lucasliano/td2project/diagrama/buzzer.png

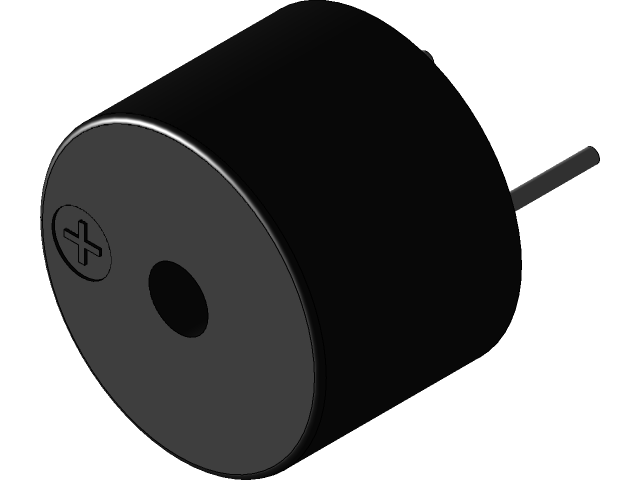
diagrama/buzzer.png
