lucasliano/td2project/diagrama/Chip RFID.png

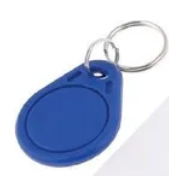
diagrama/Chip RFID.png
