lucasliano/td2project/diagrama/Diagrama-General.jpeg

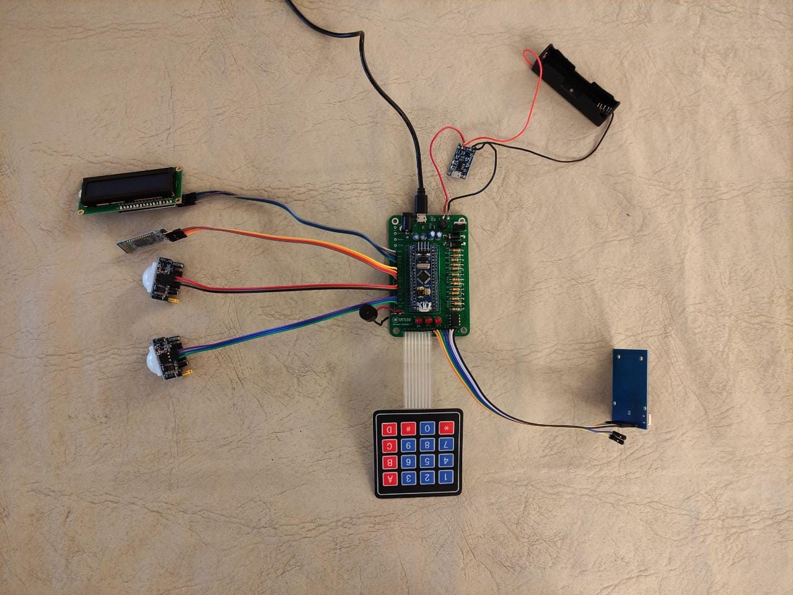
diagrama/Diagrama-General.jpeg
