lucasliano/td2project/diagrama/Diagrama-General.png

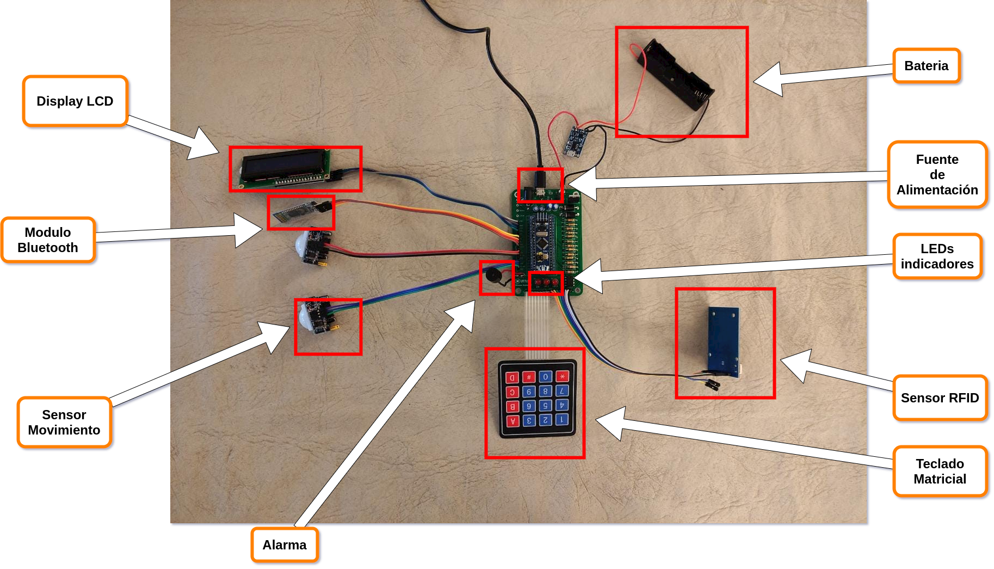
diagrama/Diagrama-General.png
