lucasliano/td2project/diagrama/Diagrama.png

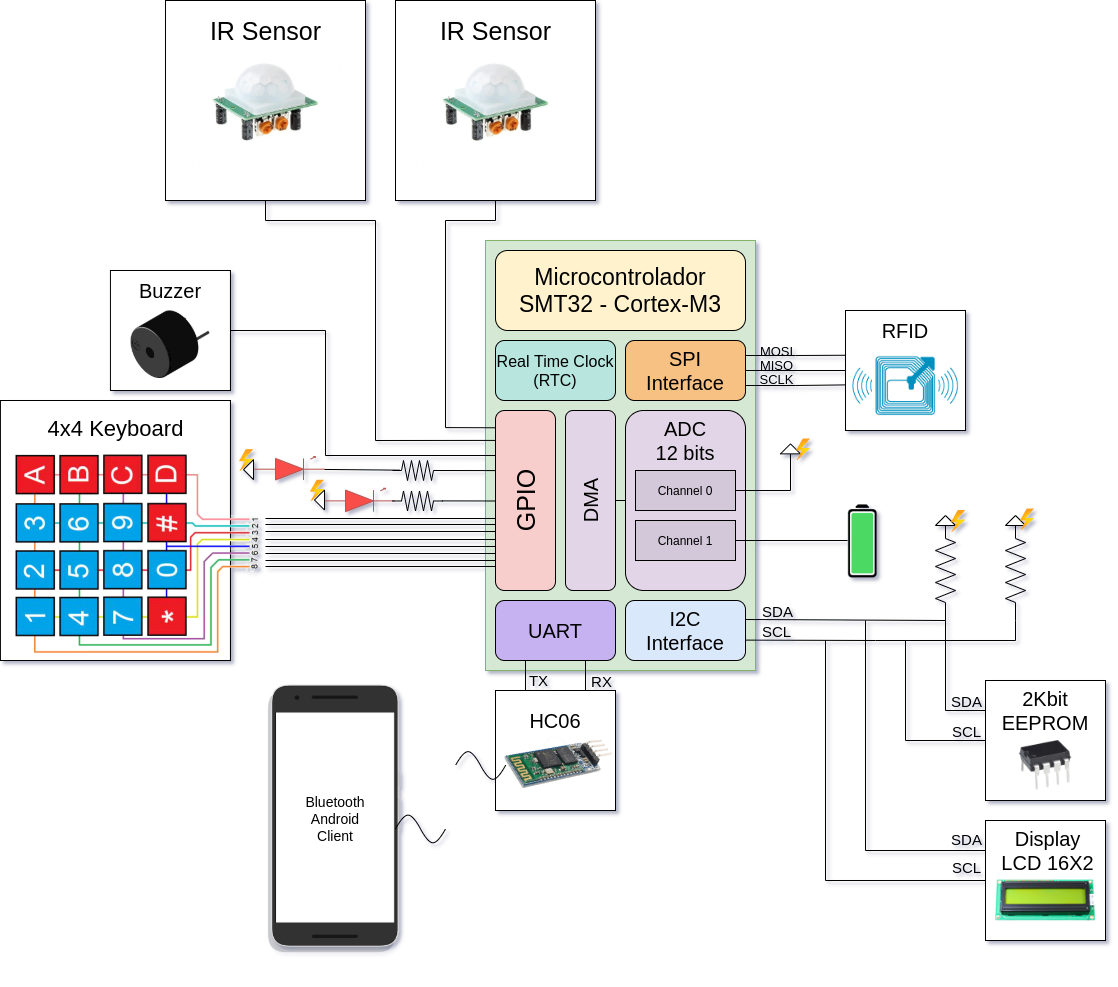
diagrama/Diagrama.png
