lucasliano/td2project/diagrama/fsm_global.png

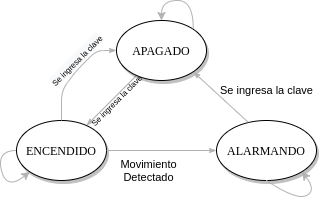
diagrama/fsm_global.png
