lucasliano/td2project/diagrama/get_mem.png

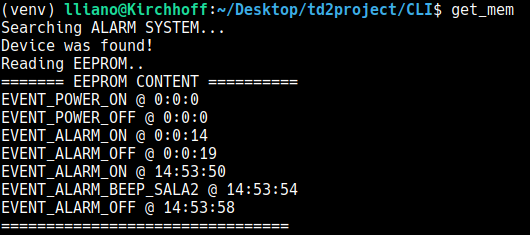
diagrama/get_mem.png
