lucasliano/td2project/diagrama/LCD.png

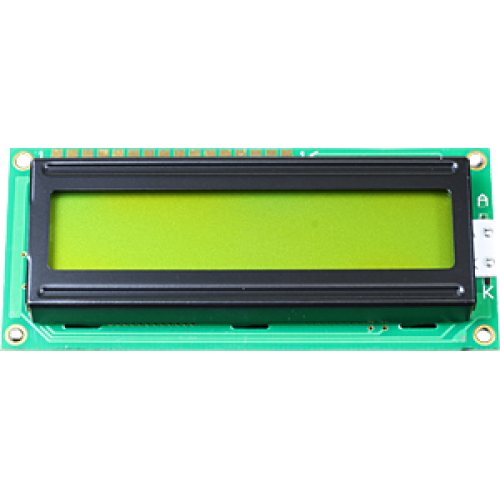
diagrama/LCD.png
