lucasliano/td2project/diagrama/MT3608.png

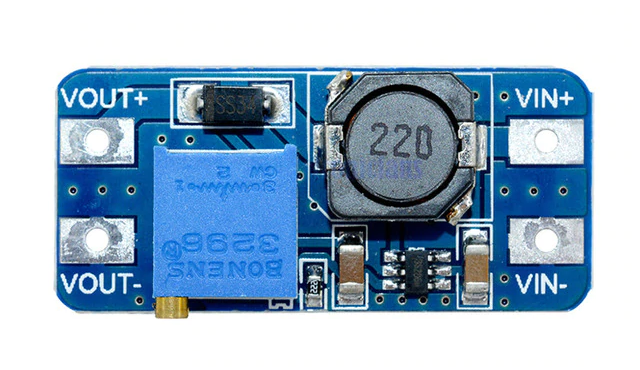
diagrama/MT3608.png
