lucasliano/td2project/diagrama/PCB-cool.jpeg

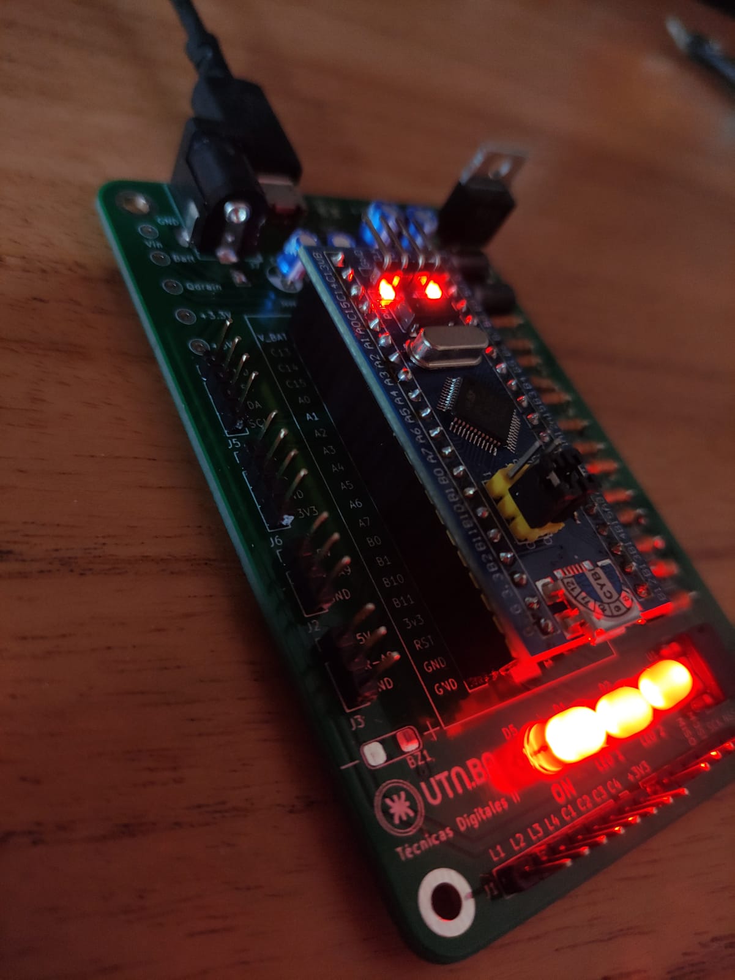
diagrama/PCB-cool.jpeg
