lucasliano/td2project/diagrama/pcb_back.png

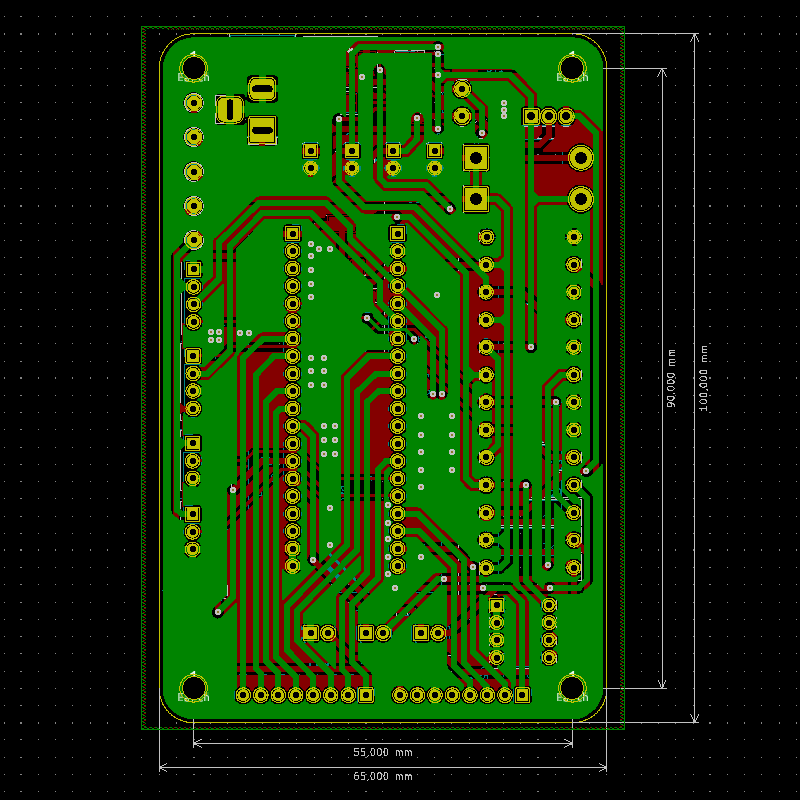
diagrama/pcb_back.png
