lucasliano/td2project/diagrama/pcb_front.png

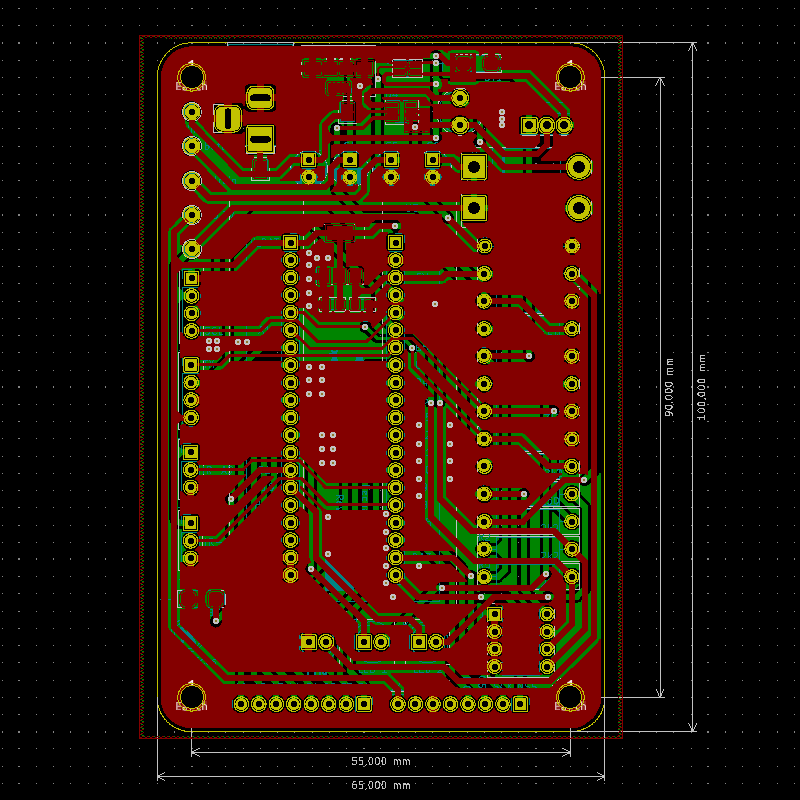
diagrama/pcb_front.png
