lucasliano/td2project/diagrama/Sensor.png

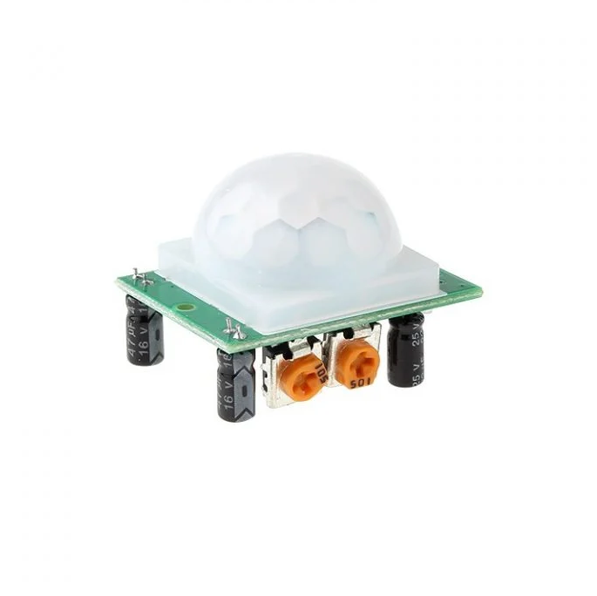
diagrama/Sensor.png
