lucasliano/td2project/diagrama/STM32.png

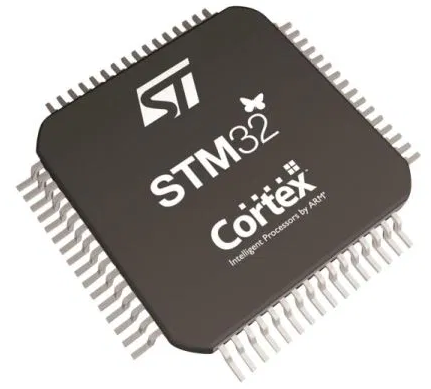
diagrama/STM32.png
