lucasliano/td2project/PCB/Comportamiento Q1.png

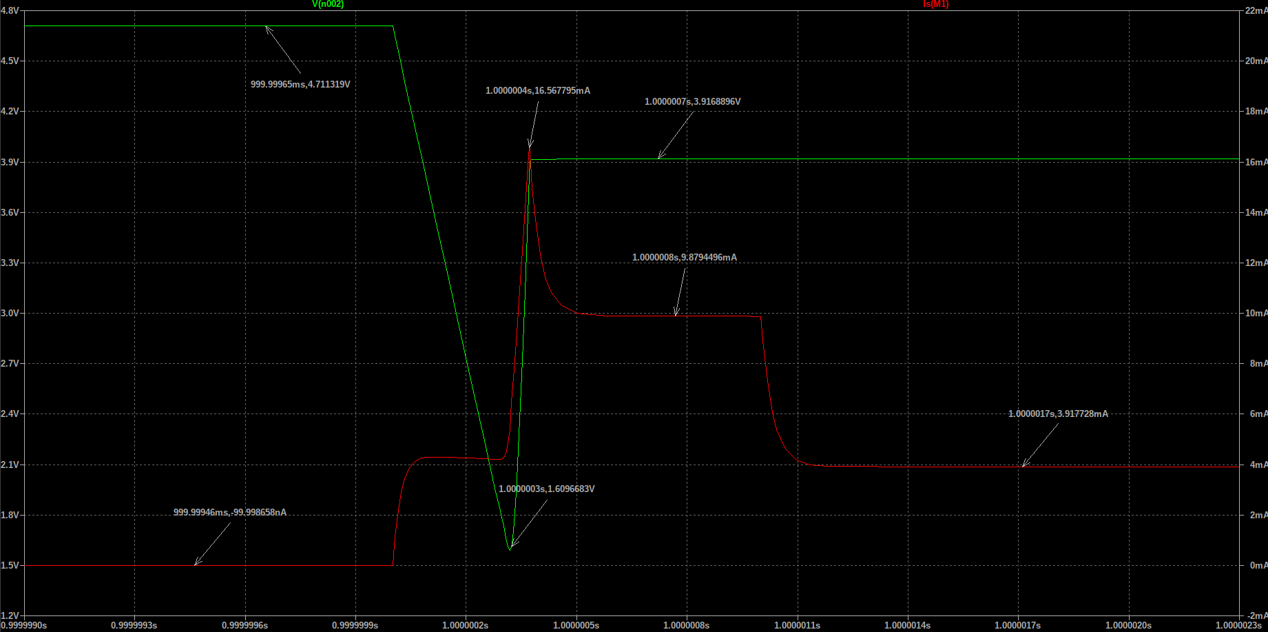
PCB/Comportamiento Q1.png
