lucasliano/td2project/PCB/project/vout_formula.png

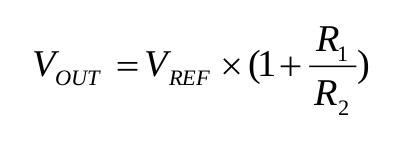
PCB/project/vout_formula.png
