lucasliano/td2project/software/Core/Inc/own_drivers.h

/**
  ******************************************************************************
  * @file           : own_drivers.h
  * @brief          : Llama a los includes de los drivers propios.
  ******************************************************************************
**/

/* Define to prevent recursive inclusion -------------------------------------*/
#ifndef __OWN_DRIVERS_H
#define __OWN_DRIVERS_H
#include <adc.h>
#include <arrebote.h>
#include <arrebote.h>
#include <eeprom.h>
#include <gpio.h>
#include <lcd.h>
#include <MFRC522.h>
#include <rtc.h>
#include <sensor.h>
#include <stdlib.h>
#include <stdio.h>
#include <string.h>
#include <hc05.h>

#include <teclado.h>

#endif /* __OWN_DRIVERS_H */
