lucasliano/td2project/software/Core/Inc/MFRC522.h

#ifndef MFRC522_H_
#define MFRC522_H_

#include "main.h"
#include "stm32f1xx_hal.h"
#include <sys/types.h>

#define SPI_NSS_Pin GPIO_PIN_12
#define SPI_NSS_GPIO_Port GPIOB

//Maximum length of the array
#define MAX_LEN 16

//MF522 Command word
#define PCD_IDLE              0x00               //NO action; Cancel the current command
#define PCD_AUTHENT           0x0E               //Authentication Key
#define PCD_RECEIVE           0x08               //Receive Data
#define PCD_TRANSMIT          0x04               //Transmit data
#define PCD_TRANSCEIVE        0x0C               //Transmit and receive data,
#define PCD_RESETPHASE        0x0F               //Reset
#define PCD_CALCCRC           0x03               //CRC Calculate

// Mifare_One card command word
# define PICC_REQIDL          0x26               // find the antenna area does not enter hibernation
# define PICC_REQALL          0x52               // find all the cards antenna area
# define PICC_ANTICOLL        0x93               // anti-collision
# define PICC_SElECTTAG       0x93               // election card
# define PICC_AUTHENT1A       0x60               // authentication key A
# define PICC_AUTHENT1B       0x61               // authentication key B
# define PICC_READ            0x30               // Read Block
# define PICC_WRITE           0xA0               // write block
# define PICC_DECREMENT       0xC0               // debit
# define PICC_INCREMENT       0xC1               // recharge
# define PICC_RESTORE         0xC2               // transfer block data to the buffer
# define PICC_TRANSFER        0xB0               // save the data in the buffer
# define PICC_HALT            0x50               // Sleep


//And MF522 The error code is returned when communication
#define MI_OK                 0
#define MI_NOTAGERR           1
#define MI_ERR                2


//------------------MFRC522 Register---------------
//Page 0:Command and Status
#define     Reserved00            0x00
#define     CommandReg            0x01
#define     CommIEnReg            0x02
#define     DivlEnReg             0x03
#define     CommIrqReg            0x04
#define     DivIrqReg             0x05
#define     ErrorReg              0x06
#define     Status1Reg            0x07
#define     Status2Reg            0x08
#define     FIFODataReg           0x09
#define     FIFOLevelReg          0x0A
#define     WaterLevelReg         0x0B
#define     ControlReg            0x0C
#define     BitFramingReg         0x0D
#define     CollReg               0x0E
#define     Reserved01            0x0F
//Page 1:Command
#define     Reserved10            0x10
#define     ModeReg               0x11
#define     TxModeReg             0x12
#define     RxModeReg             0x13
#define     TxControlReg          0x14
#define     TxAutoReg             0x15
#define     TxSelReg              0x16
#define     RxSelReg              0x17
#define     RxThresholdReg        0x18
#define     DemodReg              0x19
#define     Reserved11            0x1A
#define     Reserved12            0x1B
#define     MifareReg             0x1C
#define     Reserved13            0x1D
#define     Reserved14            0x1E
#define     SerialSpeedReg        0x1F
//Page 2:CFG
#define     Reserved20            0x20
#define     CRCResultRegM         0x21
#define     CRCResultRegL         0x22
#define     Reserved21            0x23
#define     ModWidthReg           0x24
#define     Reserved22            0x25
#define     RFCfgReg              0x26
#define     GsNReg                0x27
#define     CWGsPReg              0x28
#define     ModGsPReg             0x29
#define     TModeReg              0x2A
#define     TPrescalerReg         0x2B
#define     TReloadRegH           0x2C
#define     TReloadRegL           0x2D
#define     TCounterValueRegH     0x2E
#define     TCounterValueRegL     0x2F
//Page 3:TestRegister
#define     Reserved30            0x30
#define     TestSel1Reg           0x31
#define     TestSel2Reg           0x32
#define     TestPinEnReg          0x33
#define     TestPinValueReg       0x34
#define     TestBusReg            0x35
#define     AutoTestReg           0x36
#define     VersionReg            0x37
#define     AnalogTestReg         0x38
#define     TestDAC1Reg           0x39
#define     TestDAC2Reg           0x3A
#define     TestADCReg            0x3B
#define     Reserved31            0x3C
#define     Reserved32            0x3D
#define     Reserved33            0x3E
#define     Reserved34            0x3F
//-----------------------------------------------
// function definitions
void Write_MFRC522(u_char, u_char);
u_char Read_MFRC522(u_char);
void SetBitMask(u_char, u_char);
void ClearBitMask(u_char, u_char);
void AntennaOn();
void AntennaOff();
void MFRC522_Reset();
void MFRC522_Init(SPI_HandleTypeDef *s, GPIO_TypeDef *gpio_ss, uint16_t pin_ss);
u_char MFRC522_Request(u_char, u_char*);
u_char MFRC522_ToCard(u_char, u_char*, u_char, u_char*, uint*);
u_char MFRC522_Anticoll(u_char*);
void CalulateCRC(u_char*, u_char, u_char*);
u_char MFRC522_SelectTag(u_char*);
u_char MFRC522_Auth(u_char, u_char, u_char*, u_char*);
u_char MFRC522_Read(u_char, u_char*);
u_char MFRC522_Write(u_char, u_char*);
void MFRC522_Halt();
void MFRC522_StopCrypto1(void);

// ============ Declaraciones propias ================
#define CARD_DETECTED 0
#define CARD_NOT_FOUND 1

#define CARD_ADDED		0
#define CARD_NOT_ADDED	1

#define WAITING_CARD 	0
#define VALIDATING_CARD 1
#define REMOVING_CARD	2

#define DETECTION_TIMEOUT 1000


#define WORKING_STATE 		0
#define ADDING_CARD_STATE 	1

void rfid_toggle_state(void);
uint8_t rfid_identify_card(void);
uint8_t rfid_find_card( uint8_t* id);
uint8_t rfid_debounce(void);
uint8_t rfid_add_id(uint32_t id);

#endif /* MFRC522_H_ */
