lucasliano/td2project/software/Core/Src/lcd.c

/*
 * lcd.c
 *
 *  Created on: Oct 25, 2021
 *      Author: lliano
 */

#include <own_drivers.h>

/* ========= Variables Globales ==============*/
/* ---------     Semaforos        ------------*/

/* ---------  Colas de mensaje    ------------*/

/* ---------  Variables de estado ------------*/
static I2C_HandleTypeDef* i2c;
/* ===========================================*/



void lcd_init (I2C_HandleTypeDef *s)
{
	i2c = s;

	// 4 bit initialization
	HAL_Delay(50);  		// wait for >40ms
	lcd_send_cmd (0x30);
	HAL_Delay(5);  			// wait for >4.1ms
	lcd_send_cmd (0x30);
	HAL_Delay(1);  			// wait for >100us
	lcd_send_cmd (0x30);
	HAL_Delay(10);
	lcd_send_cmd (0x20);  	// 4bit mode
	HAL_Delay(10);

	// display initialization
	lcd_send_cmd (0x28); 	// Function set --> DL=0 (4 bit mode), N = 1 (2 line display) F = 0 (5x8 characters)
	HAL_Delay(1);
	lcd_send_cmd (0x08); 	//Display on/off control --> D=0,C=0, B=0  ---> display off
	HAL_Delay(1);
	lcd_send_cmd (0x01);  	// clear display
	HAL_Delay(1);
	HAL_Delay(1);
	lcd_send_cmd (0x06); 	//Entry mode set --> I/D = 1 (increment cursor) & S = 0 (no shift)
	HAL_Delay(1);
	lcd_send_cmd (0x0C); 	//Display on/off control --> D = 1, C and B = 0. (Cursor and blink, last two bits)
	lcd_clear ();
}

void lcd_send_cmd (char cmd)
{
  char data_u, data_l;
	uint8_t data_t[4];
	data_u = (cmd&0xf0);
	data_l = ((cmd<<4)&0xf0);
	data_t[0] = data_u|0x0C;  //en=1, rs=0
	data_t[1] = data_u|0x08;  //en=0, rs=0
	data_t[2] = data_l|0x0C;  //en=1, rs=0
	data_t[3] = data_l|0x08;  //en=0, rs=0
	HAL_I2C_Master_Transmit (i2c, LCD_ADDRESS_I2C,(uint8_t *) data_t, 4, 100);
}


void lcd_send_data (char data)
{
	char data_u, data_l;
	uint8_t data_t[4];
	data_u = (data&0xf0);
	data_l = ((data<<4)&0xf0);
	data_t[0] = data_u|0x0D;  //en=1, rs=1
	data_t[1] = data_u|0x09;  //en=0, rs=1
	data_t[2] = data_l|0x0D;  //en=1, rs=1
	data_t[3] = data_l|0x09;  //en=0, rs=1
	HAL_I2C_Master_Transmit (i2c, LCD_ADDRESS_I2C,(uint8_t *) data_t, 4, 100);
}

void lcd_clear (void)
{
	lcd_send_cmd (0x01);  // clear display
}

void lcd_cursor(int row, int col)
{
    switch (row)
    {
        case 0:
            col |= 0x80;
            break;
        case 1:
            col |= 0xC0;
            break;
    }

    lcd_send_cmd (col);
}

void lcd_send_string (char* str, uint8_t size)
{
	uint8_t dato;
	for(uint8_t i = 0; i < size ; i++)
	{
		dato = str[i];
		lcd_send_data (dato);
	}
}
